ikatkov/battery-capacity-meter/ltspice/tl431-analog-switch.asc

C3: cap; 10µ
M1: nmos; AO6408
R1: res; 1.333k
R3: res; 800
R7: res; 300
R10: res; 2k
U1: tl431
V1: voltage; 5
V2: VOLTAGE; PULSE(0 5 15m 40u 40u 50m 1000)
Named nets: 0, VCC, V1, 2.5V
.tran 0 100m 10m
.inc TL431.lib
Vin must be same or higher
than charger voltage
1W
min voltage 12V
max voltage 30V
sets battery max voltage
