ikatkov/battery-capacity-meter/ltspice/discharge.asc

C1: cap; 1n
R1: res; 1k
R2: res; 18.5k
R3: res; 81.5k
R4: res; 1
R5: res; 100
R7: res; 47k
U2: opamp2; LM358_AB
U3: tip142
V1: voltage; 5
V2: voltage; 1.1
Named nets: DAC, 0, VCC
.inc LM358_AB.sub
.tran 0 100m 0
3.5W
100k trimmer
