ikatkov/battery-capacity-meter/ltspice/opamp-offset-compensation.asc

R1: res; 1k
R2: res; 18.5k
R3: res; 81.5k
R7: res; 47k
U2: opamp2; LM358_AB
V1: voltage; 5
V2: voltage; 1.1
Named nets: ref, 0, VCC
.inc LM358_AB.sub
.tran 0 100m 0
100k trimmer
